Logo66/AuraBip/hardware/project/final_bottom.png

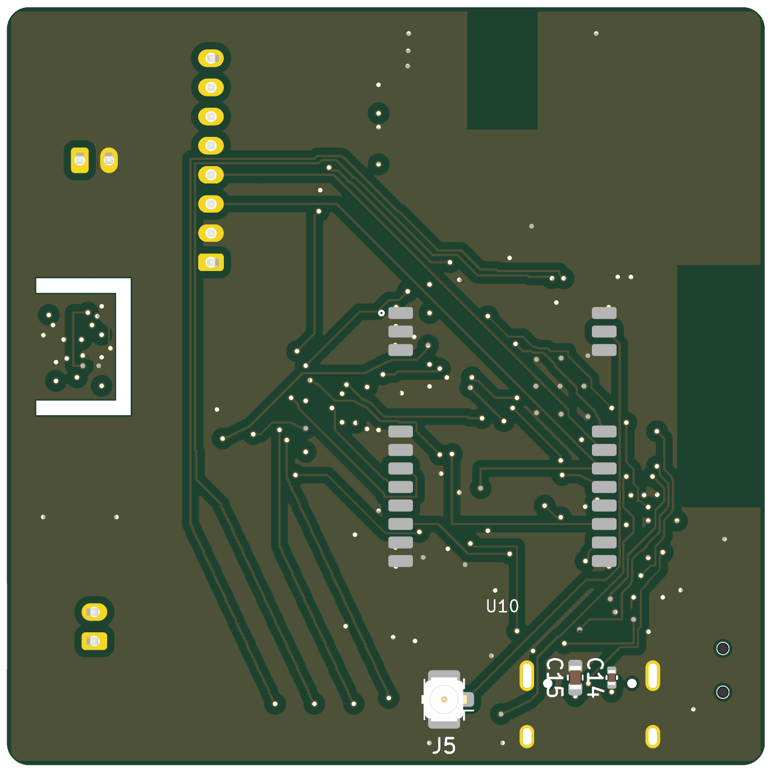
hardware/project/final_bottom.png
