Logo66/AuraBip/hardware/project/final_top.png

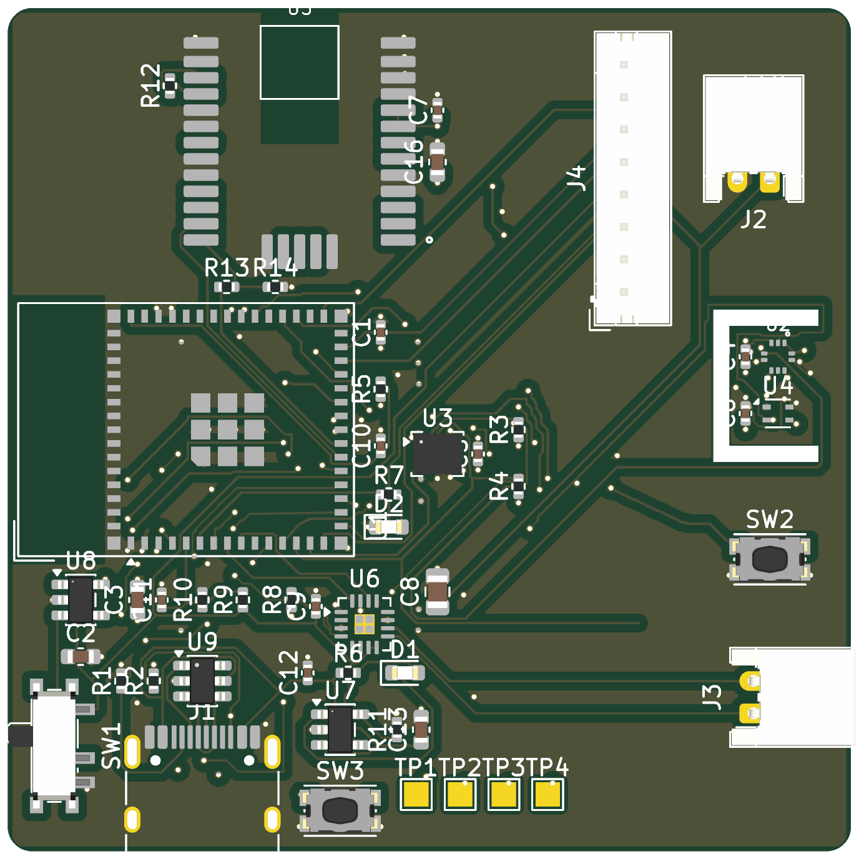
hardware/project/final_top.png
