Logo66/AuraBip/hardware/project/news_persp.png

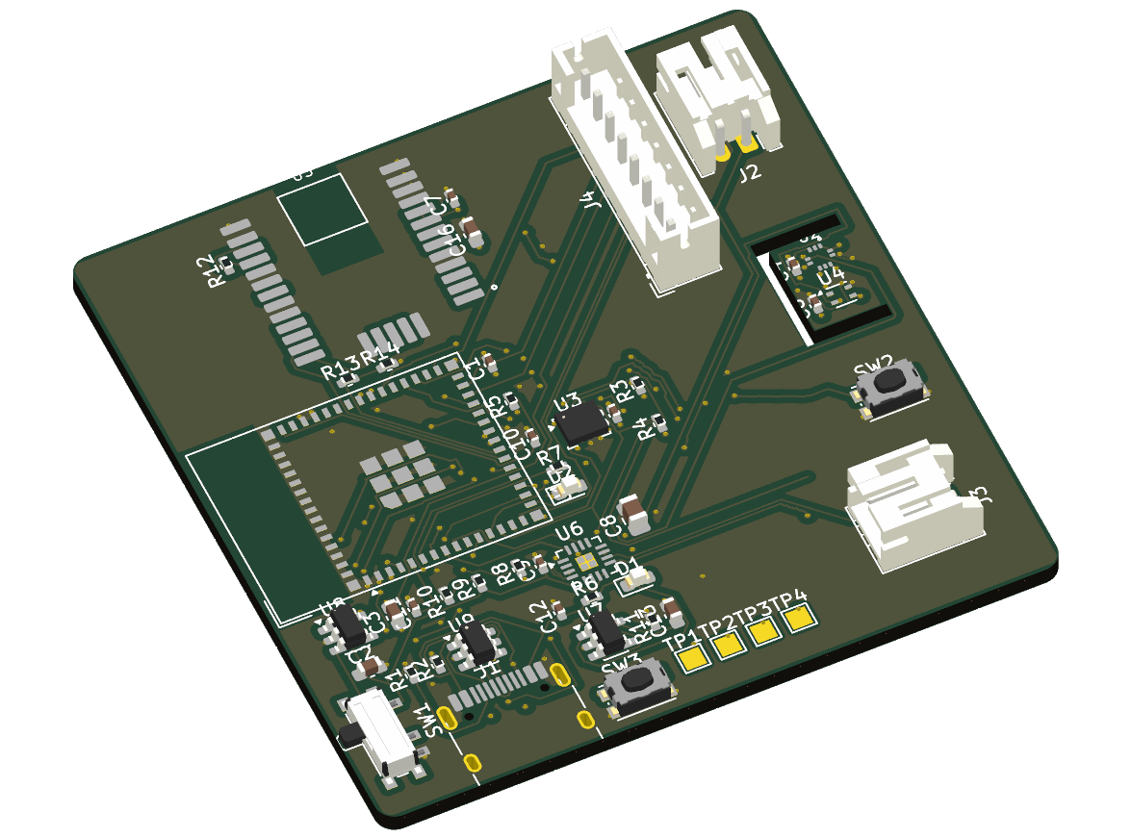
hardware/project/news_persp.png
