Logo66/AuraBip/hardware/project/news_top.png

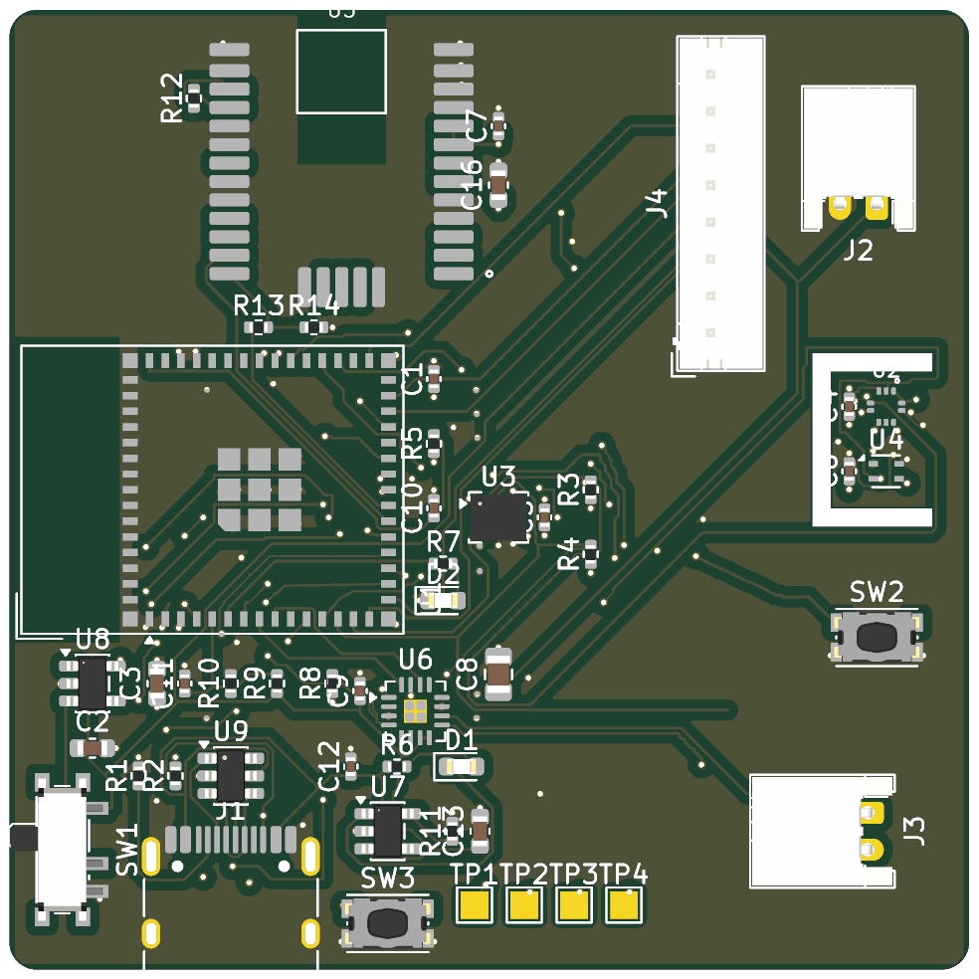
hardware/project/news_top.png
