Logo66/AuraBip/hardware/project/render_top.png

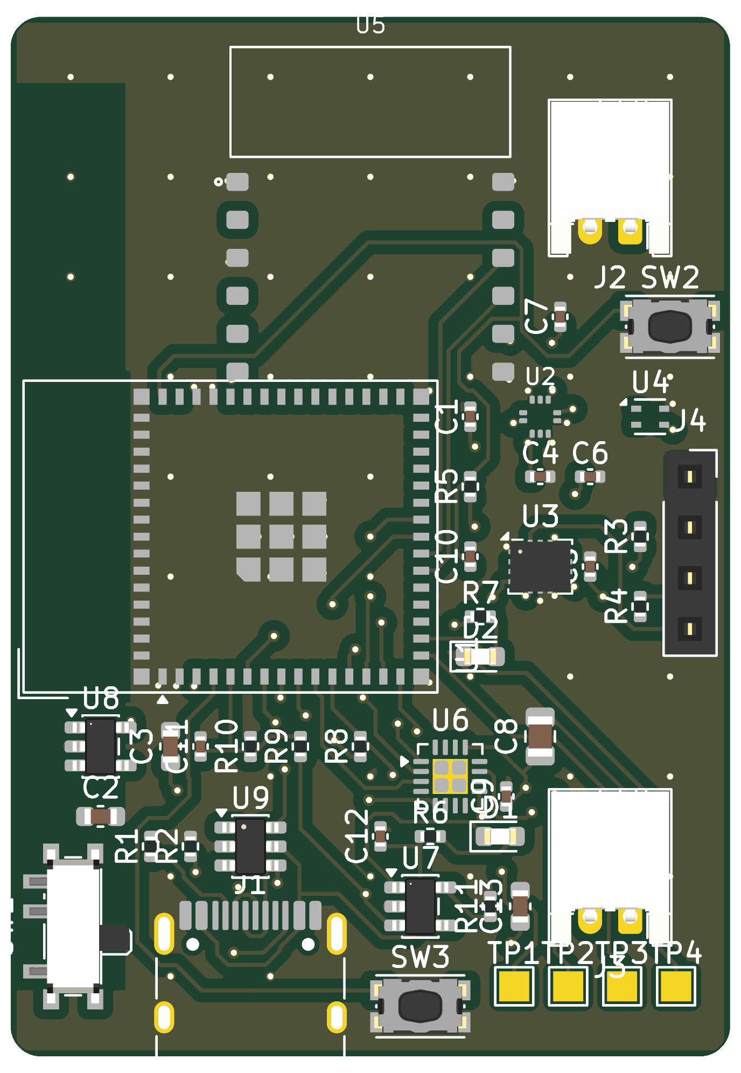
hardware/project/render_top.png
